NCSU-Libraries/card-system/on-system-content/granted.gif

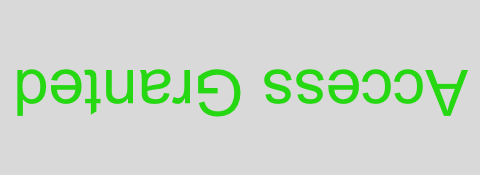
on-system-content/granted.gif
