NCSU-Libraries/card-system/on-system-content/config.py

#!/usr/bin/python
# -*- coding: utf-8 -*-
#
# config.py
#
# Private/implementation specific configuration variables.

# Space Auth API constants
API_Users_URL = 'https://API.URL'
API_Key = 'APIKEY'

Unique_Name_Key = 'unique_name'
ID_Key = 'id'

Space_Access_Unique_Name = 'space_access'
Space_Access_ID = '1'

# Google Sheets constants
Data_Spreadsheet = 'SPREADSHEET_NAME'
Credentials_File = '/path/to/credentials.json'
